slu4coder/Minimal-UART-CPU-System/Revisions 1.3 - 1.6 (FLASH)/Revision 1.5 (Expanded)/KiCAD/ClockAndReset.sch

## KiCad design Revisions 1.3 - 1.6 (FLASH)/Revision 1.5 (Expanded)/KiCAD/ClockAndReset.sch (2021-06-06)

Schematic: ClockAndReset.sch

Parts:
D3: 5V; LED_D3.0mm
J2: CPU CLOCK; PinHeader_2x05_P2.54mm_Vertical
R1: 4.7k; R_Axial_DIN0207_L6.3mm_D2.5mm_P7.62mm_Horizontal
R13: 1k; R_Axial_DIN0207_L6.3mm_D2.5mm_P7.62mm_Horizontal
SW1: RESET; SW_PUSH_6mm
U2: 74HC161; DIP-16_W7.62mm
X1: 3.6864MHz; Oscillator_DIP-14

Notes on the sheet:
A 7.3728MHz crystal may also be used with a divider of 2 or higher.
